niclabs/water-monitoring/2. Hito Homologación/all_ec/data/README.md

# 2020-10-22 EC data series

- `2020-10-22_real_ec.csv`: Real EC value (given by the calibration solution)
- `2020-10-22_data_ECGravity.csv`: Analog value from Gravity: Analog Electrical Conductivity Sensor (read from ADC, value in mV)
- `2020-10-22_data_TDSGravity1.csv`: Analog value from DFRobot Gravity: Analog TDS Sensor #1 (read from ADC, value in mV)
- `2020-10-22_data_TDSGravity2.csv`: Analog value from DFRobot Gravity: Analog TDS Sensor #2 (read from ADC, value in mV)
- `2020-10-22_data_multiparametro.csv`: EC value from Hach multiparameter sensor.
