niclabs/water-monitoring/2. Hito Homologación/all_ec/data3/README.md

# 2020-11-02 EC data series
`2020-11-02_tds.csv` columns:
- `N`: Row number.
- `MultiP.1`: EC value from Hach multiparameter sensor measured at the same solution as DFRobot Gravity: Analog TDS Sensor #1.
- `TDS.1`: Analog value from DFRobot Gravity: Analog TDS Sensor #1 (read from ADC, value in mV).
- `MultiP.2`: EC value from Hach multiparameter sensor measured at the same solution as DFRobot Gravity: Analog TDS Sensor #2.
- `TDS.2`: Analog value from DFRobot Gravity: Analog TDS Sensor #2 (read from ADC, value in mV).
- `T1`: Temperature (°C) value from Hach multiparameter sensor measured at the same solution as DFRobot Gravity: Analog TDS Sensor #1.
- `T2`: Temperature (°C) value from Hach multiparameter sensor measured at the same solution as DFRobot Gravity: Analog TDS Sensor #2.
- `Sol`: Calibration solution used at the data point (optional, in uS/cm)
- `Comm`: Comment
