niclabs/water-monitoring/2. Hito Homologación/all_temperature/data/README.md

# All temperature data
- `2020-10-07_all_temperature.txt`: Temperature (°C) measured with the multiparameter (reference)
- `2020-10-07_data_sensores_homologacion.csv`: Measured data (t [ms] since start, temperature by sensors, ADC read from thermistor)
