niclabs/water-monitoring/2. Hito Homologación/all_ec/data2/plot_tds_fit_ec_vs_ec.png

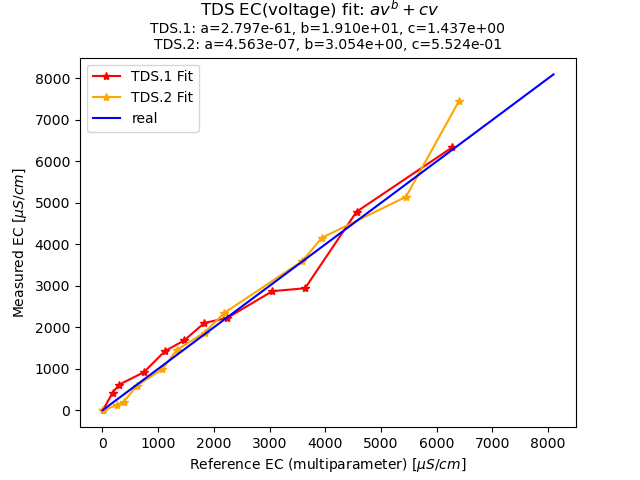
2. Hito Homologación/all_ec/data2/plot_tds_fit_ec_vs_ec.png
