niclabs/water-monitoring/2. Hito Homologación/all_ec/data/affine_plot_abserr_vs_time.png

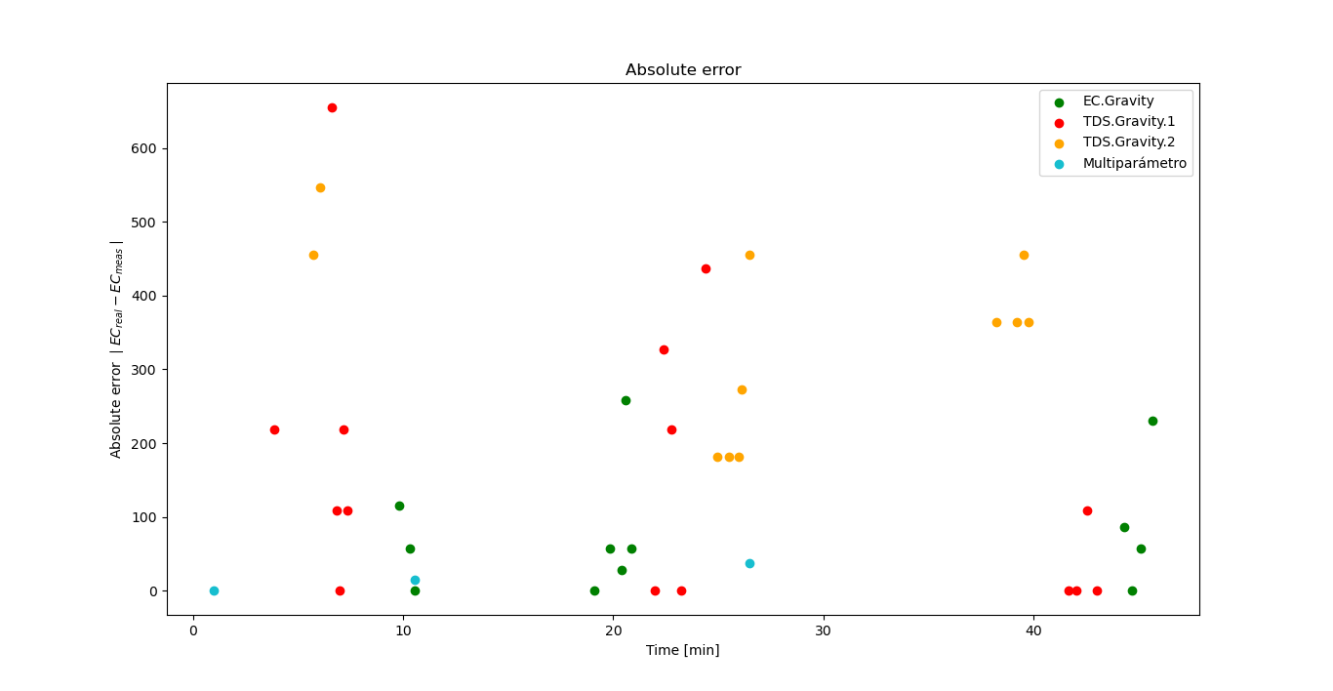
2. Hito Homologación/all_ec/data/affine_plot_abserr_vs_time.png
