niclabs/water-monitoring/2. Hito Homologación/all_ec/data/affine_plot_ec_err_comparison.png

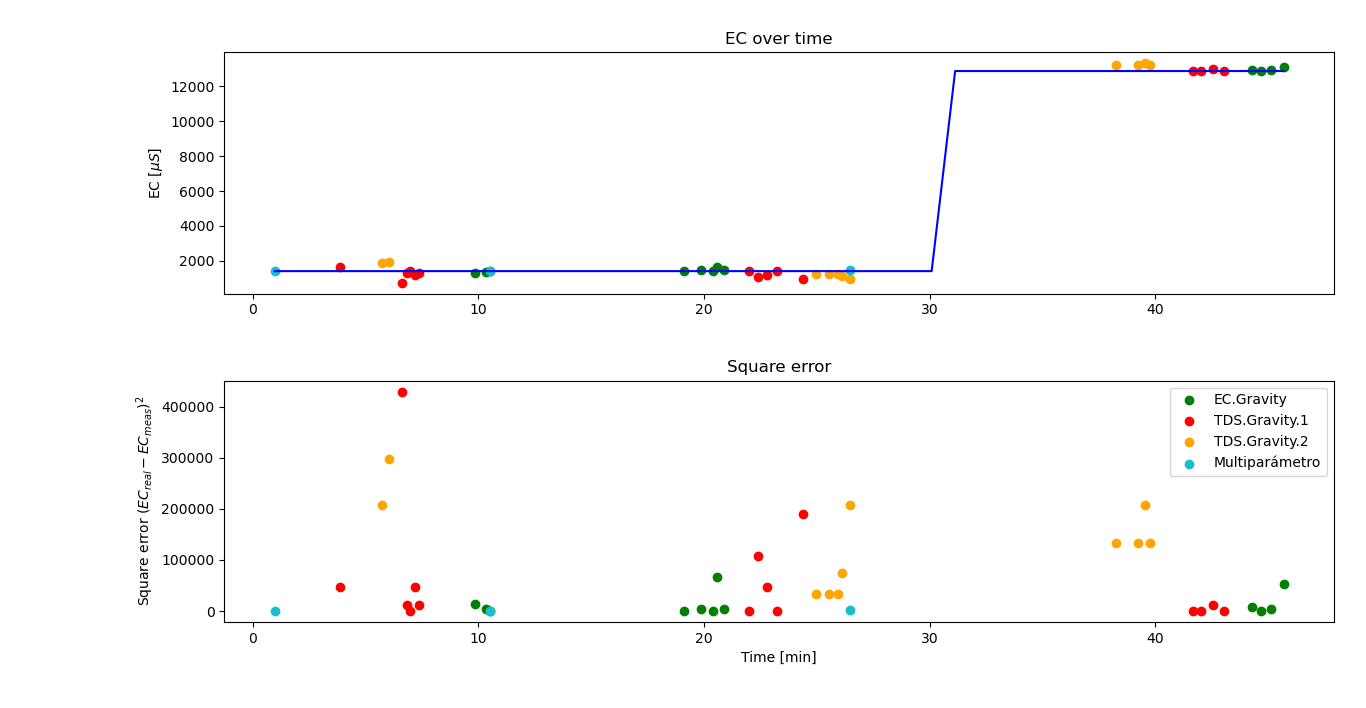
2. Hito Homologación/all_ec/data/affine_plot_ec_err_comparison.png
