niclabs/water-monitoring/2. Hito Homologación/all_ec/data/affine_plot_ec_vs_ec.png

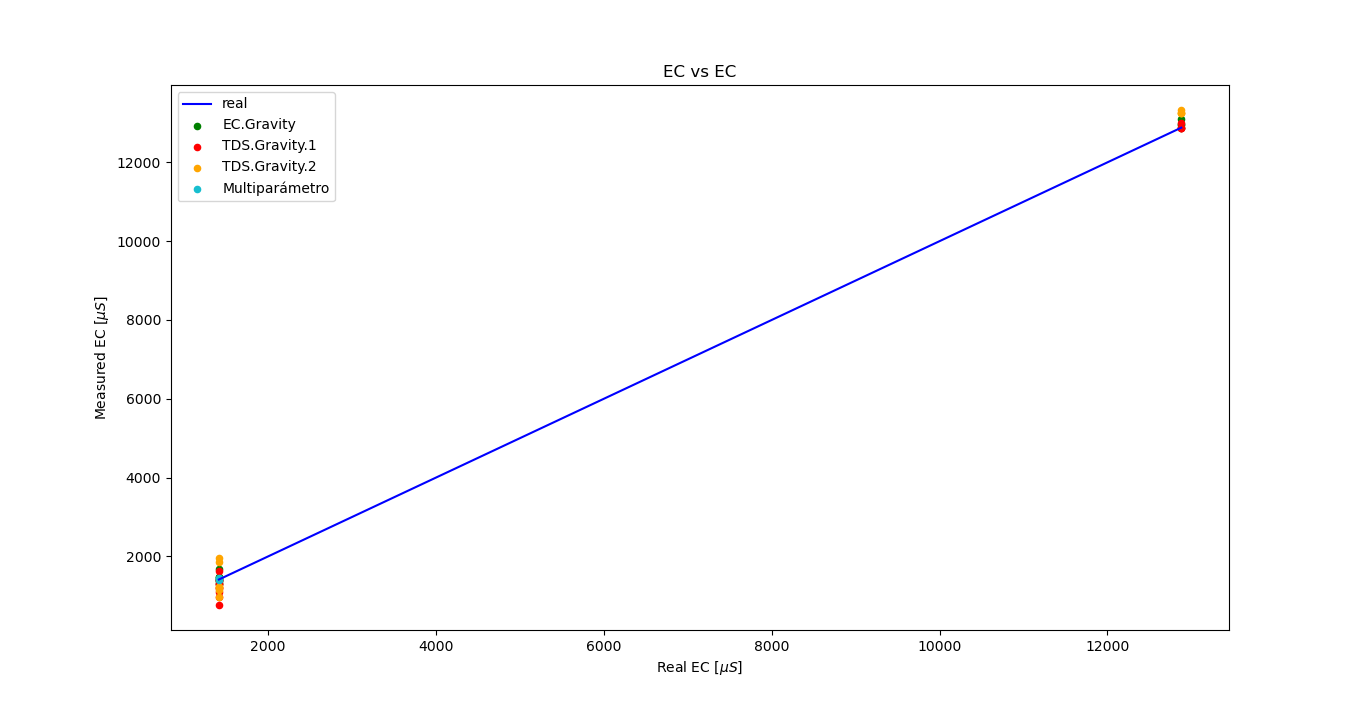
2. Hito Homologación/all_ec/data/affine_plot_ec_vs_ec.png
