niclabs/water-monitoring/2. Hito Homologación/all_ec/data/plot_ec_vs_ec_low.png

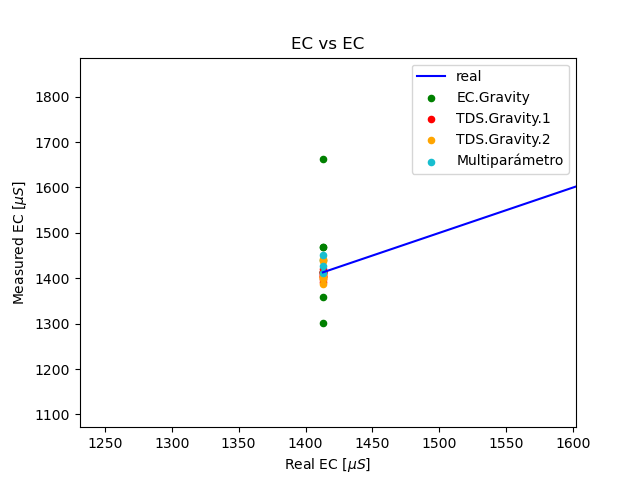
2. Hito Homologación/all_ec/data/plot_ec_vs_ec_low.png
