niclabs/water-monitoring/2. Hito Homologación/all_ec/data/plot_err_vs_time.png

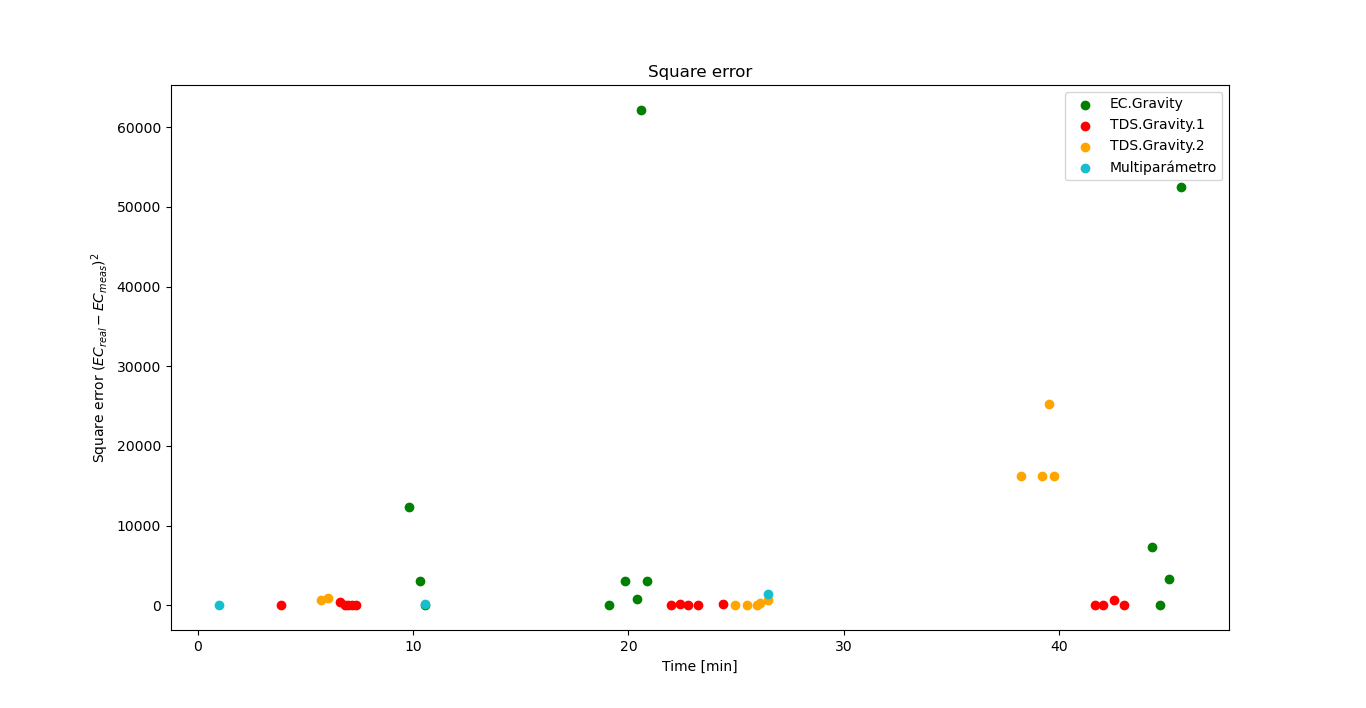
2. Hito Homologación/all_ec/data/plot_err_vs_time.png
