niclabs/water-monitoring/2. Hito Homologación/all_ph/data/plot_ph_vs_ph.png

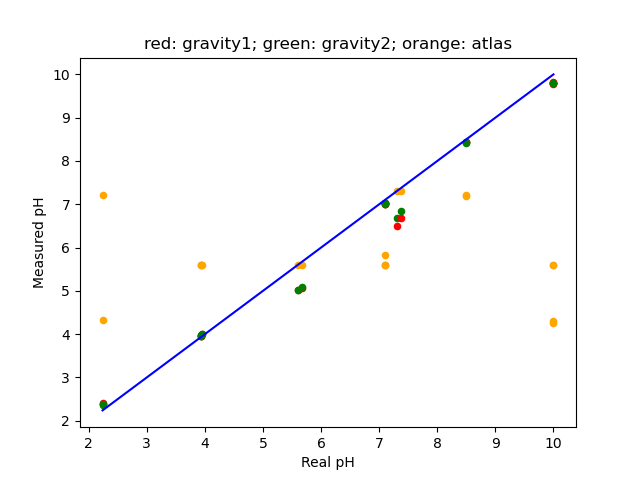
2. Hito Homologación/all_ph/data/plot_ph_vs_ph.png
