niclabs/water-monitoring/2. Hito Homologación/all_temperature/data/plot_temp_vs_temp.png

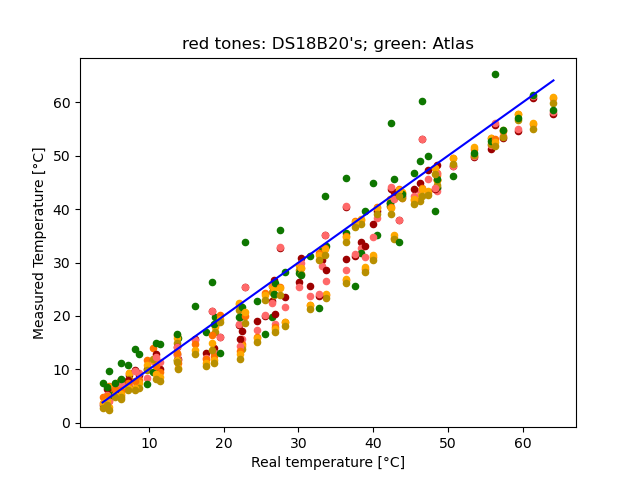
2. Hito Homologación/all_temperature/data/plot_temp_vs_temp.png
