niclabs/water-monitoring/3. Hito Energía/current_data/img/arduino_5m_5v_base.png

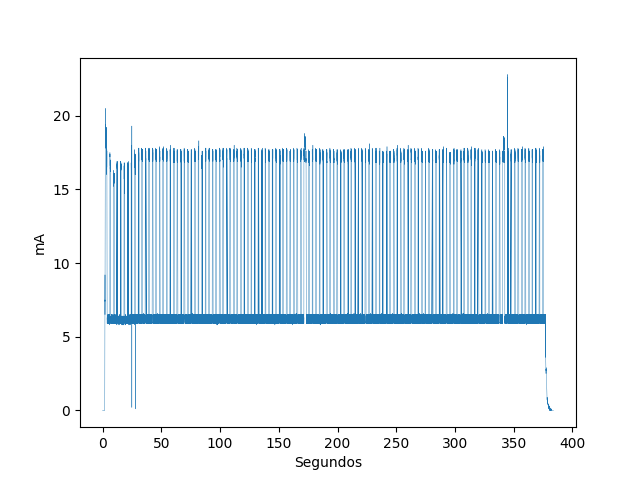
3. Hito Energía/current_data/img/arduino_5m_5v_base.png
