niclabs/water-monitoring/3. Hito Energía/current_data/img/arduino_5m_5v_rep.png

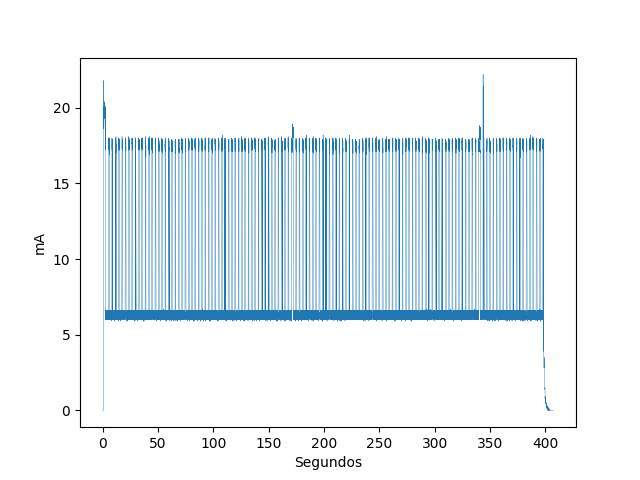
3. Hito Energía/current_data/img/arduino_5m_5v_rep.png
