niclabs/water-monitoring/3. Hito Energía/current_data/img/corriente_5m_5v_dif.png

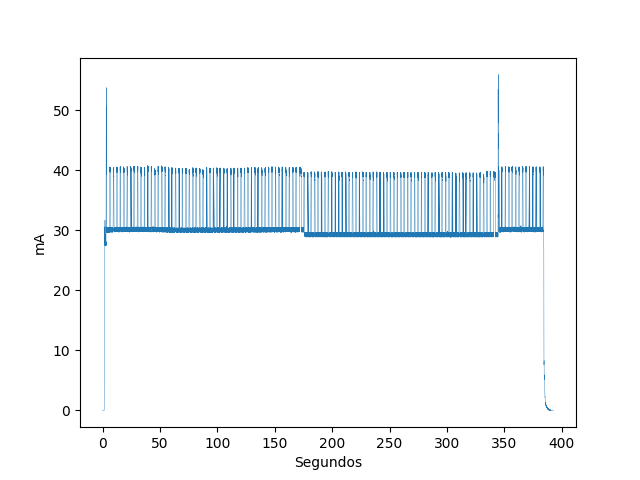
3. Hito Energía/current_data/img/corriente_5m_5v_dif.png
