niclabs/water-monitoring/3. Hito Energía/current_data/img/ds18b20_5m_5v_base.png

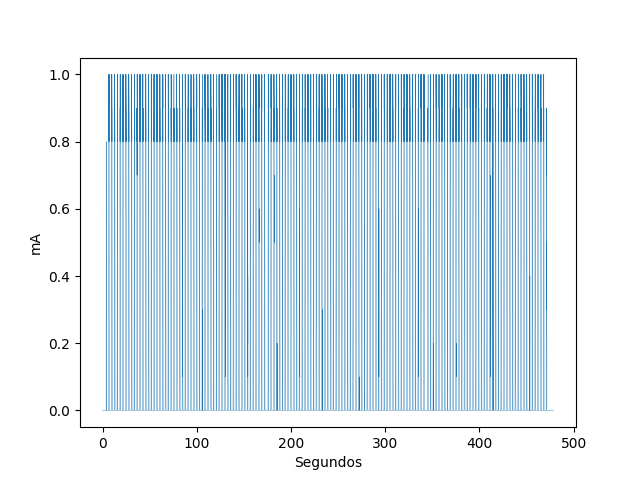
3. Hito Energía/current_data/img/ds18b20_5m_5v_base.png
