niclabs/water-monitoring/3. Hito Energía/current_data/img/fib_sleep.png

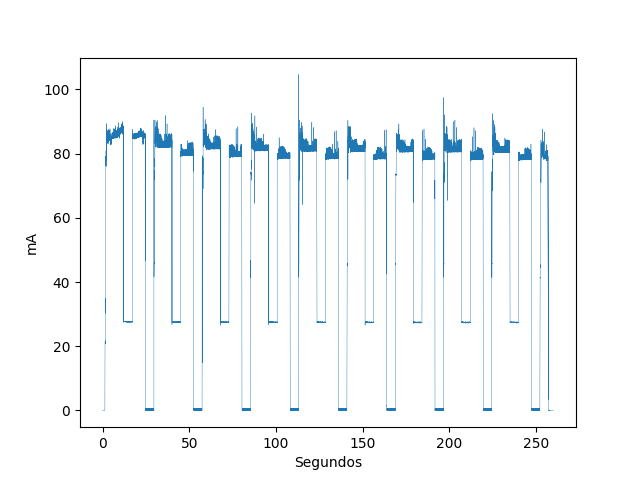
3. Hito Energía/current_data/img/fib_sleep.png
