niclabs/water-monitoring/3. Hito Energía/current_data/img/lopy_5m_5v.png

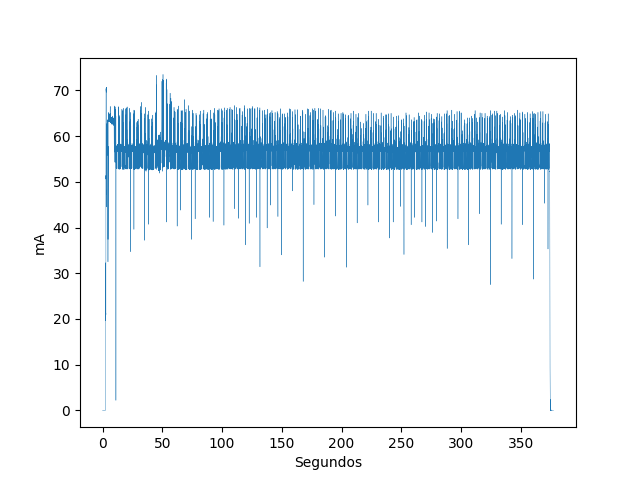
3. Hito Energía/current_data/img/lopy_5m_5v.png
