niclabs/water-monitoring/3. Hito Energía/current_data/img/lopy_5v_dif.png

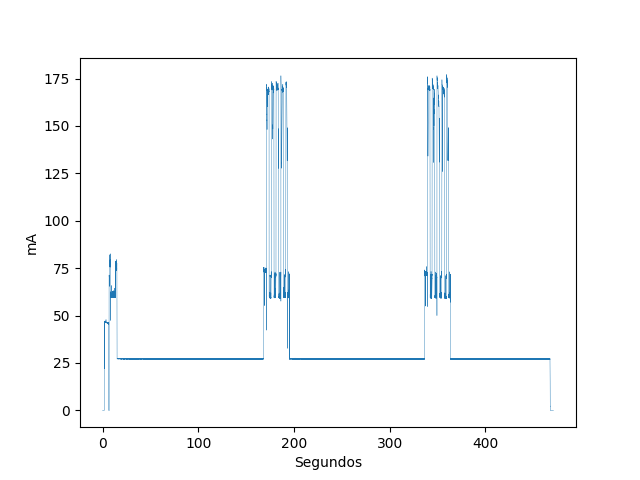
3. Hito Energía/current_data/img/lopy_5v_dif.png
