niclabs/water-monitoring/3. Hito Energía/current_data/img/lopy_envio_dif.png

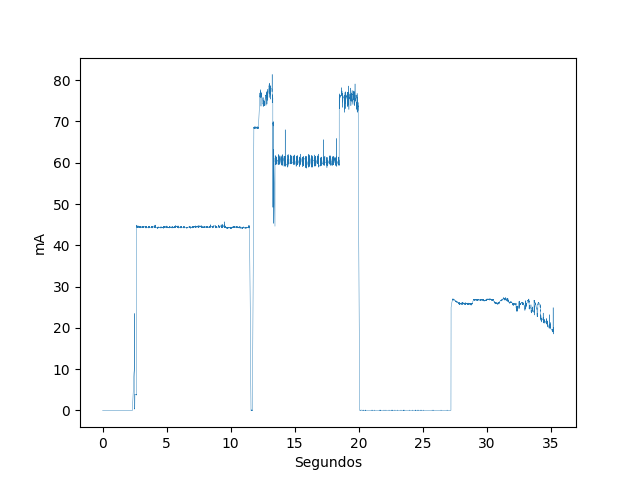
3. Hito Energía/current_data/img/lopy_envio_dif.png
