niclabs/water-monitoring/3. Hito Energía/current_data/img/rtc_5m_5v_base.png

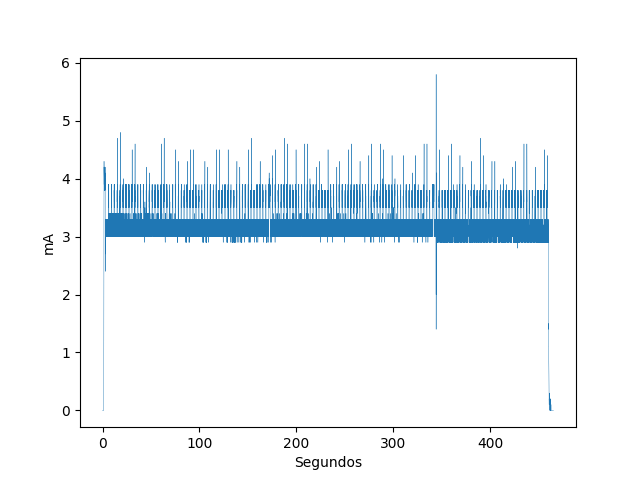
3. Hito Energía/current_data/img/rtc_5m_5v_base.png
