niclabs/water-monitoring/3. Hito Energía/current_data/img/sleep_lopy.png

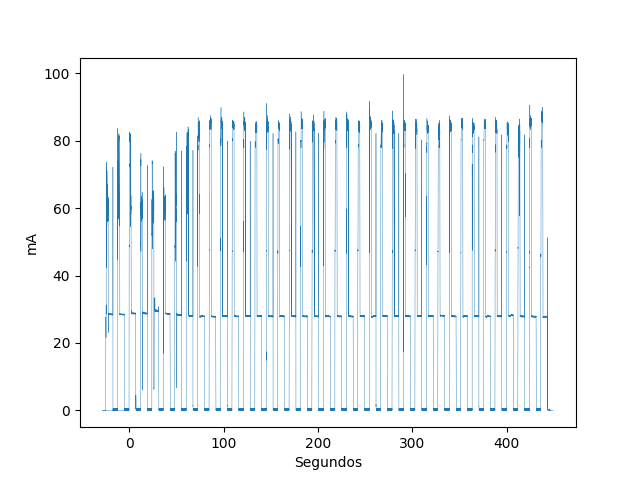
3. Hito Energía/current_data/img/sleep_lopy.png
