niclabs/water-monitoring/5. Hito Carcasa/2. Visualizaciones/Baterias.JPG

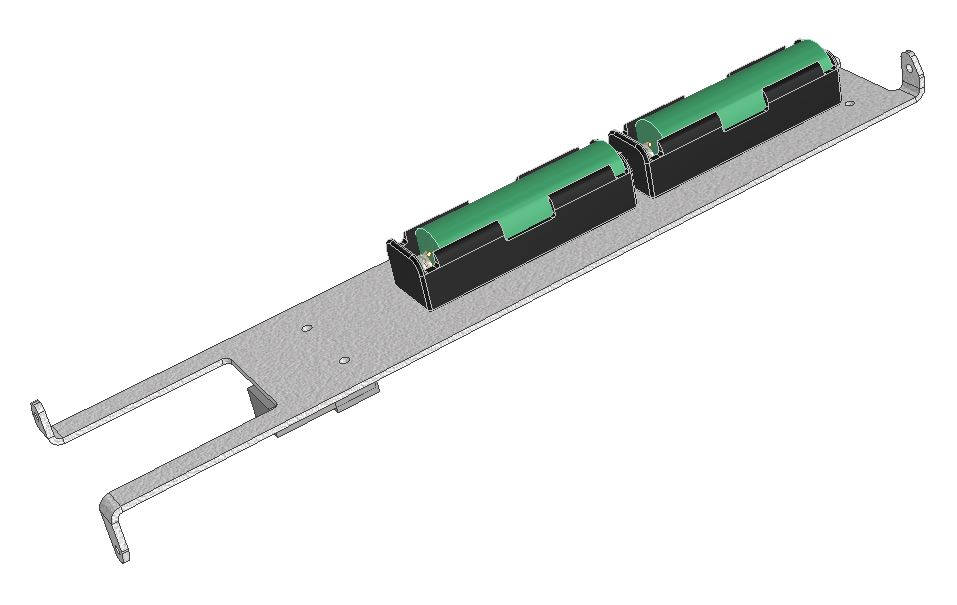
5. Hito Carcasa/2. Visualizaciones/Baterias.JPG
