niclabs/water-monitoring/5. Hito Carcasa/2. Visualizaciones/Enganche Sello.JPG

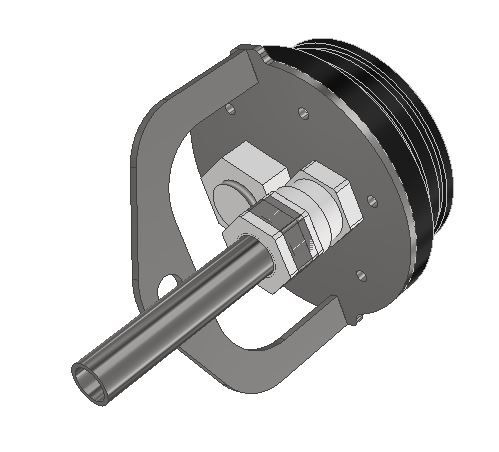
5. Hito Carcasa/2. Visualizaciones/Enganche Sello.JPG
