niclabs/water-monitoring/5. Hito Carcasa/2. Visualizaciones/Enganche.JPG

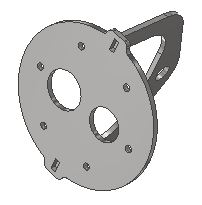
5. Hito Carcasa/2. Visualizaciones/Enganche.JPG
