niclabs/water-monitoring/5. Hito Carcasa/2. Visualizaciones/Estopa manguera.JPG

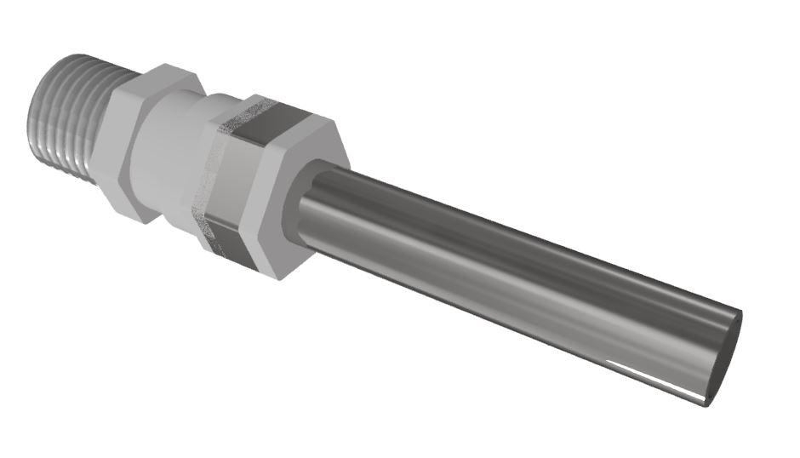
5. Hito Carcasa/2. Visualizaciones/Estopa manguera.JPG
