niclabs/water-monitoring/5. Hito Carcasa/2. Visualizaciones/Estopas enganche.JPG

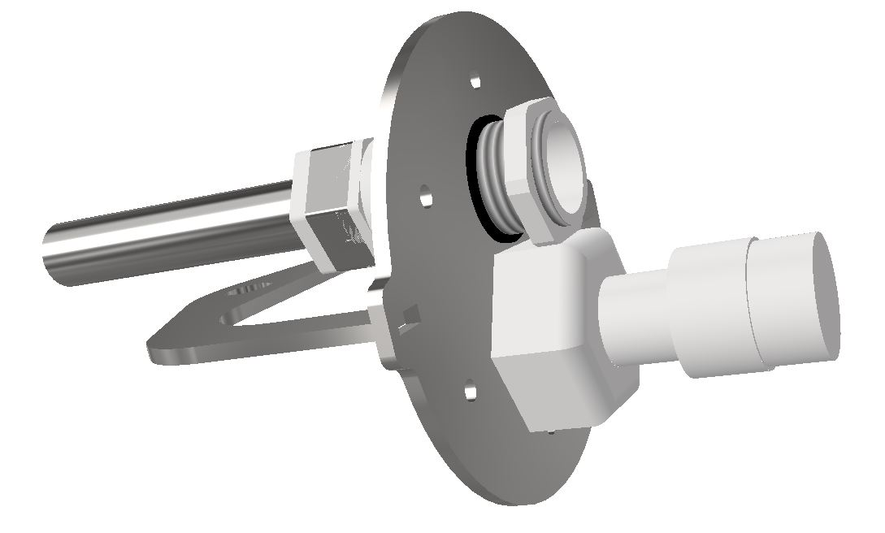
5. Hito Carcasa/2. Visualizaciones/Estopas enganche.JPG
