niclabs/water-monitoring/5. Hito Carcasa/2. Visualizaciones/Manguera Ajuste.JPG

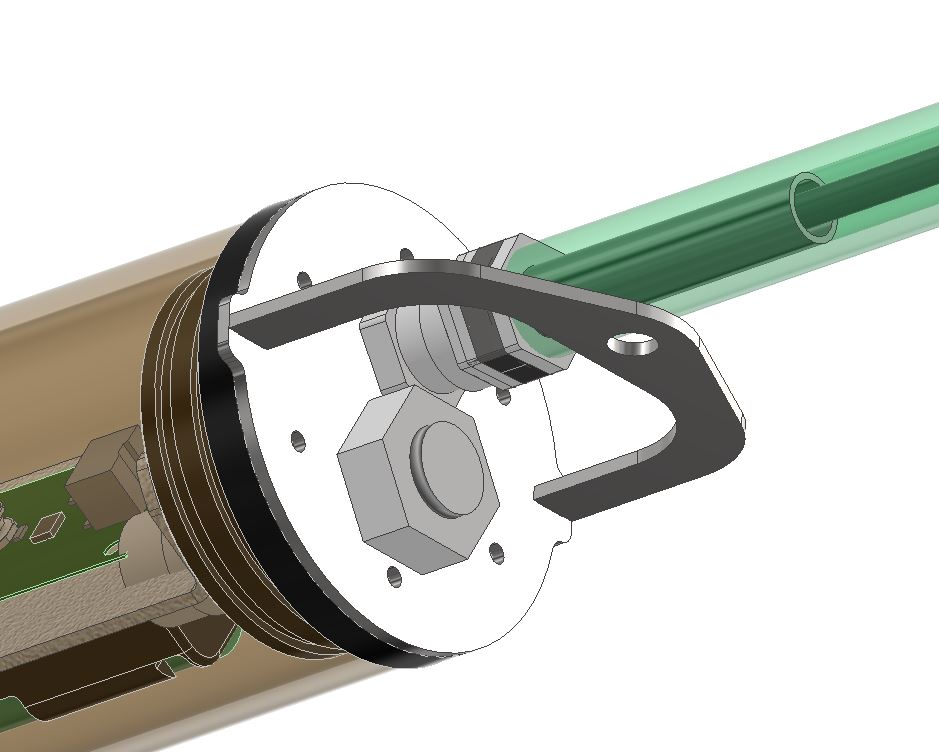
5. Hito Carcasa/2. Visualizaciones/Manguera Ajuste.JPG
