niclabs/water-monitoring/5. Hito Carcasa/2. Visualizaciones/Plataforma.JPG

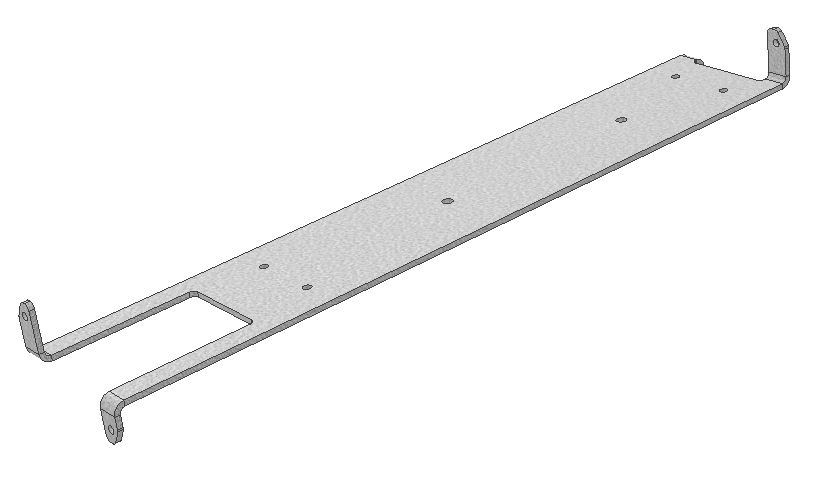
5. Hito Carcasa/2. Visualizaciones/Plataforma.JPG
