niclabs/water-monitoring/5. Hito Carcasa/2. Visualizaciones/Proteccion sello.JPG

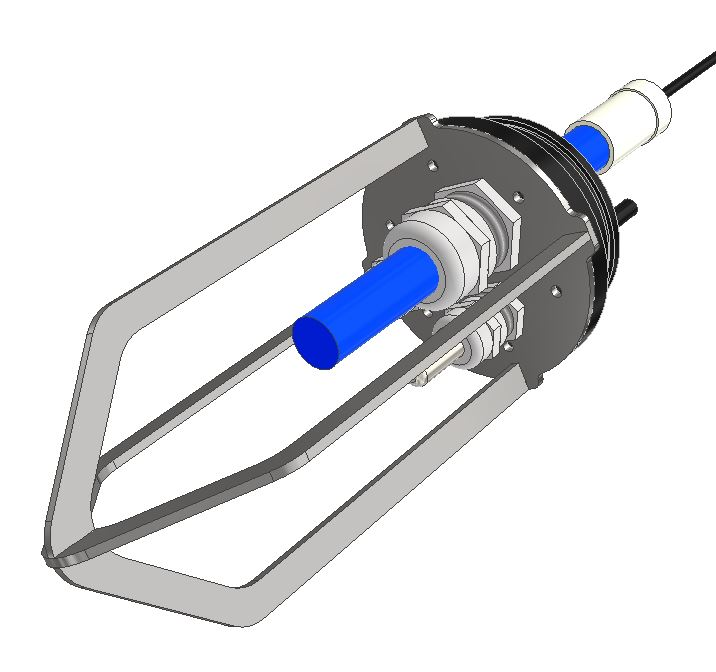
5. Hito Carcasa/2. Visualizaciones/Proteccion sello.JPG
