niclabs/water-monitoring/5. Hito Carcasa/2. Visualizaciones/Protecciขn Estopas.JPG

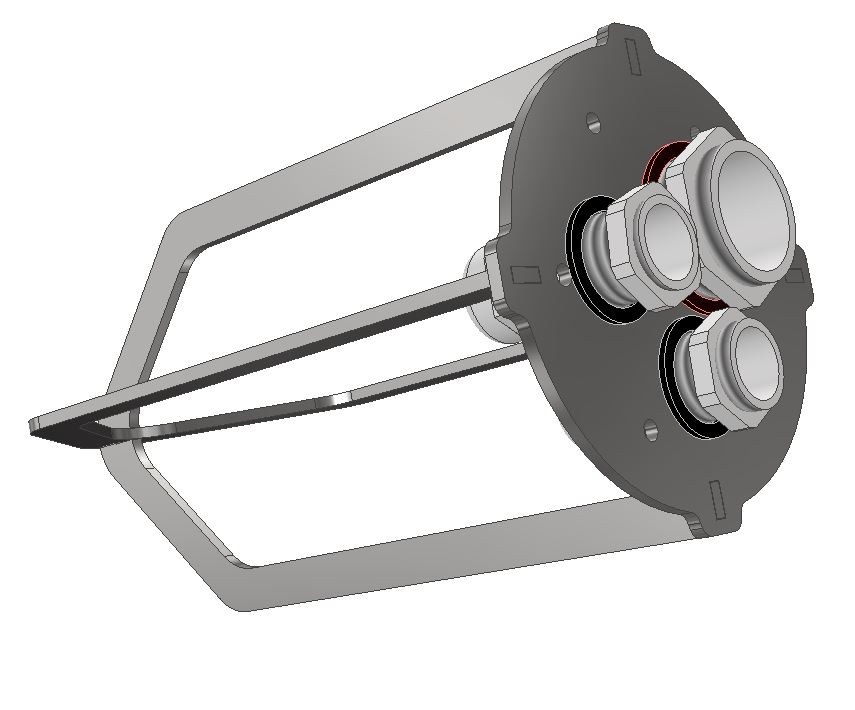
5. Hito Carcasa/2. Visualizaciones/Protecciขn Estopas.JPG
