niclabs/water-monitoring/5. Hito Carcasa/2. Visualizaciones/Protecciขn.JPG

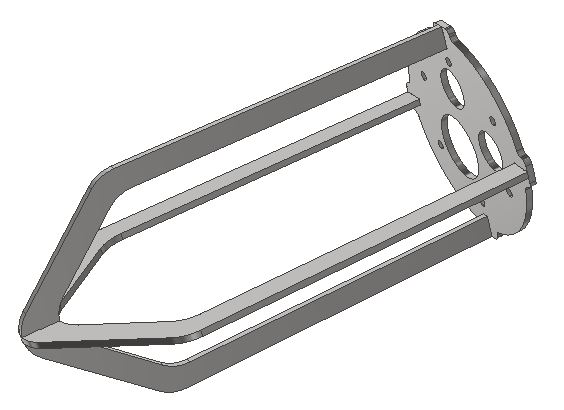
5. Hito Carcasa/2. Visualizaciones/Protecciขn.JPG
