niclabs/water-monitoring/5. Hito Carcasa/2. Visualizaciones/Sello Protrecciขn.JPG

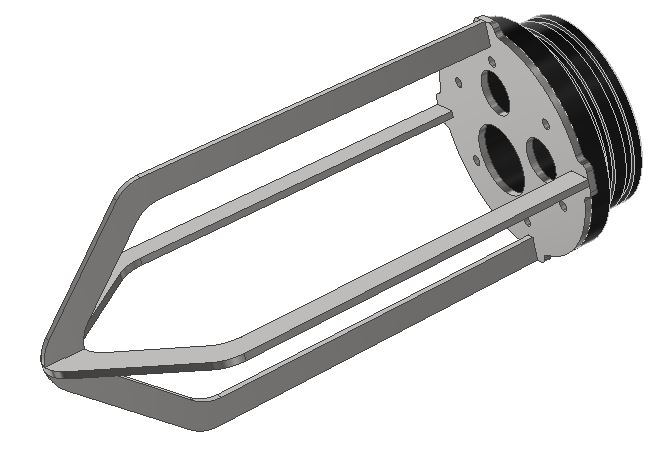
5. Hito Carcasa/2. Visualizaciones/Sello Protrecciขn.JPG
