niclabs/water-monitoring/5. Hito Carcasa/2. Visualizaciones/Sellos.JPG

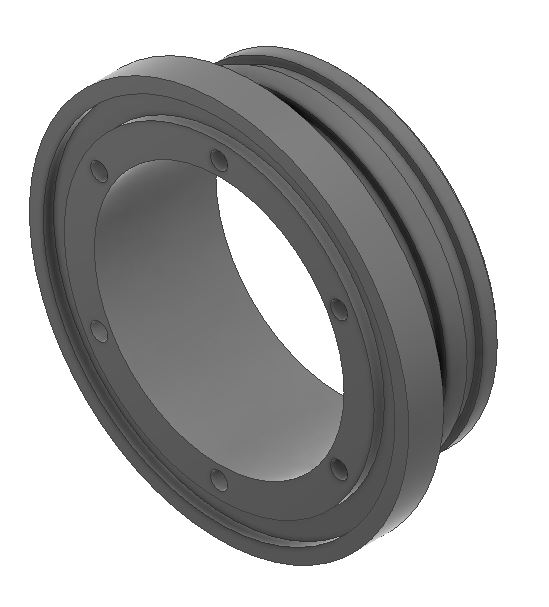
5. Hito Carcasa/2. Visualizaciones/Sellos.JPG
