niclabs/water-monitoring/5. Hito Carcasa/2. Visualizaciones/Sensores estopas.JPG

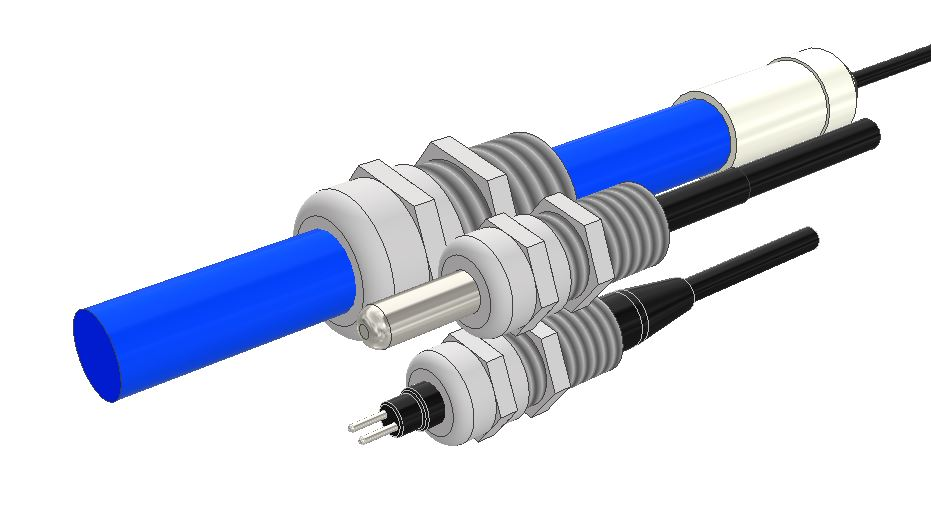
5. Hito Carcasa/2. Visualizaciones/Sensores estopas.JPG
