niclabs/water-monitoring/5. Hito Carcasa/2. Visualizaciones/Sensores Proteccion.JPG

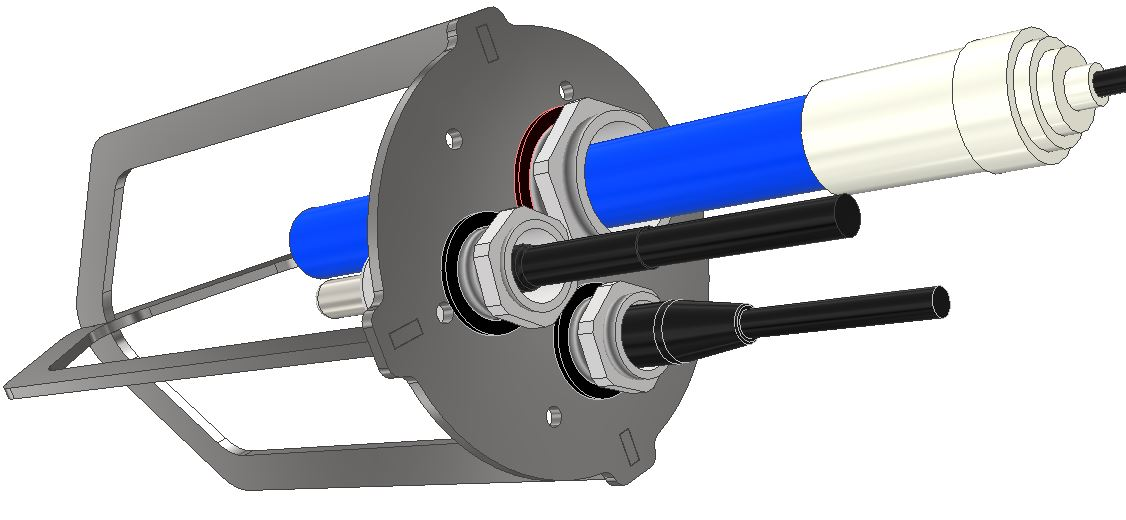
5. Hito Carcasa/2. Visualizaciones/Sensores Proteccion.JPG
