niclabs/water-monitoring/5. Hito Carcasa/2. Visualizaciones/Tubo.JPG

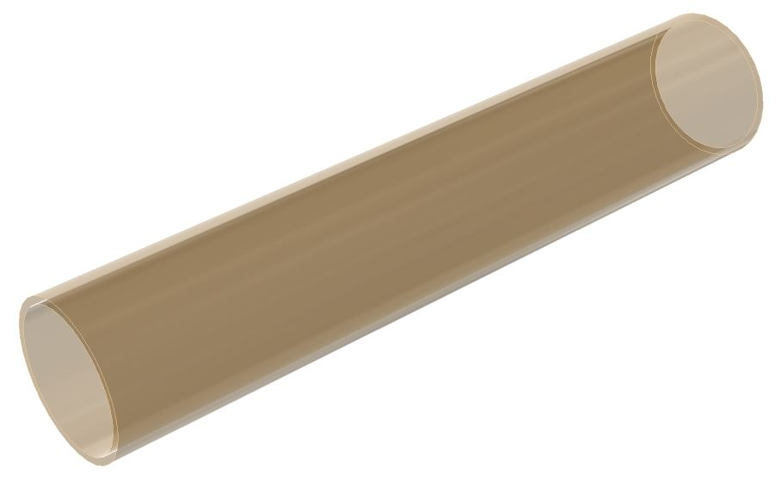
5. Hito Carcasa/2. Visualizaciones/Tubo.JPG
