niclabs/water-monitoring/docs/images/carcasa_prototipo_0.jpg

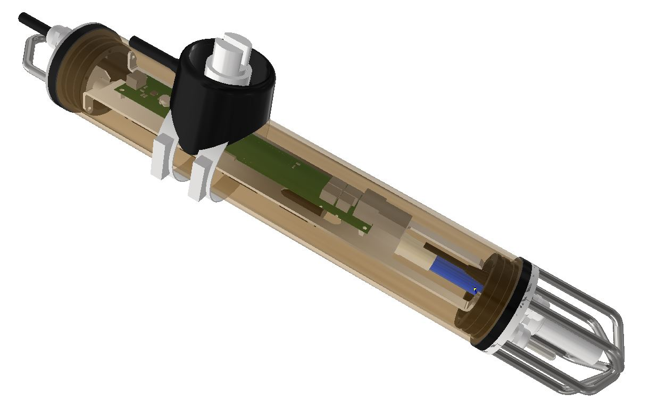
docs/images/carcasa_prototipo_0.jpg
