niclabs/water-monitoring/docs/images/carcasa_validacion_4.jpg

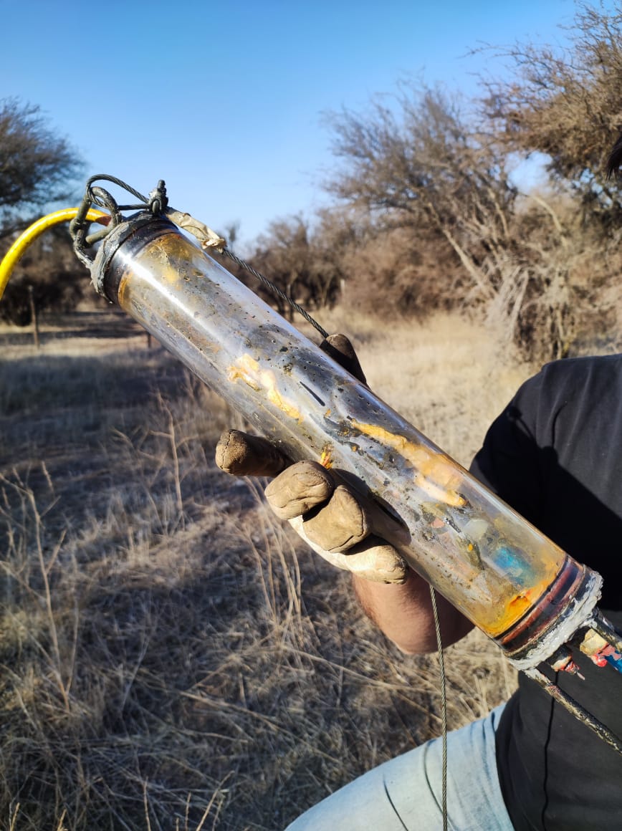
docs/images/carcasa_validacion_4.jpg
