niclabs/water-monitoring/5. Hito Carcasa/1. Planos fabricación de piezas/3. Soldaduras_Piezas acero inoxidable/Imagen referencia Enganche Flat V6.JPG

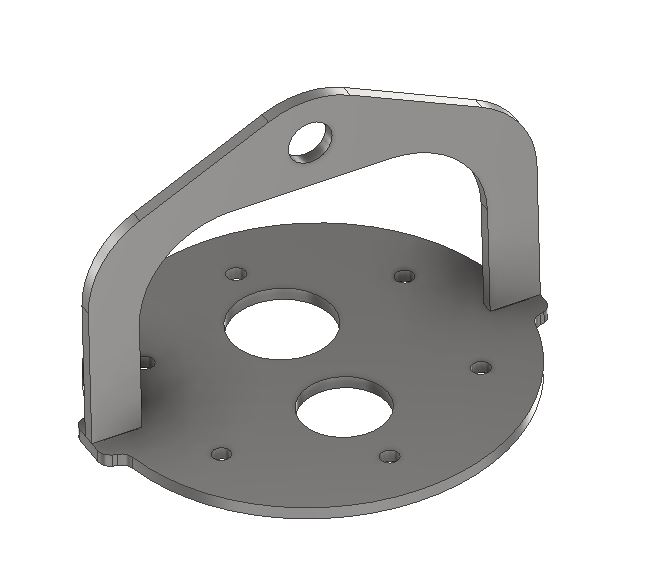
5. Hito Carcasa/1. Planos fabricación de piezas/3. Soldaduras_Piezas acero inoxidable/Imagen referencia Enganche Flat V6.JPG
