niclabs/water-monitoring/5. Hito Carcasa/1. Planos fabricación de piezas/3. Soldaduras_Piezas acero inoxidable/Union Manguera - imagen.jpeg

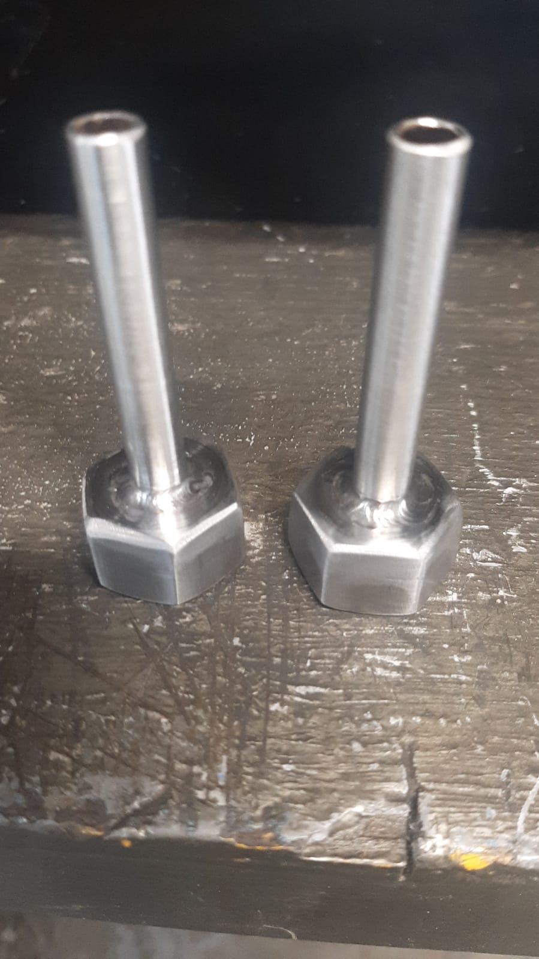
5. Hito Carcasa/1. Planos fabricación de piezas/3. Soldaduras_Piezas acero inoxidable/Union Manguera - imagen.jpeg
