niclabs/water-monitoring/5. Hito Carcasa/1. Planos fabricación de piezas/5. Caja de montaje exterior/Distribución electrónica caja.png

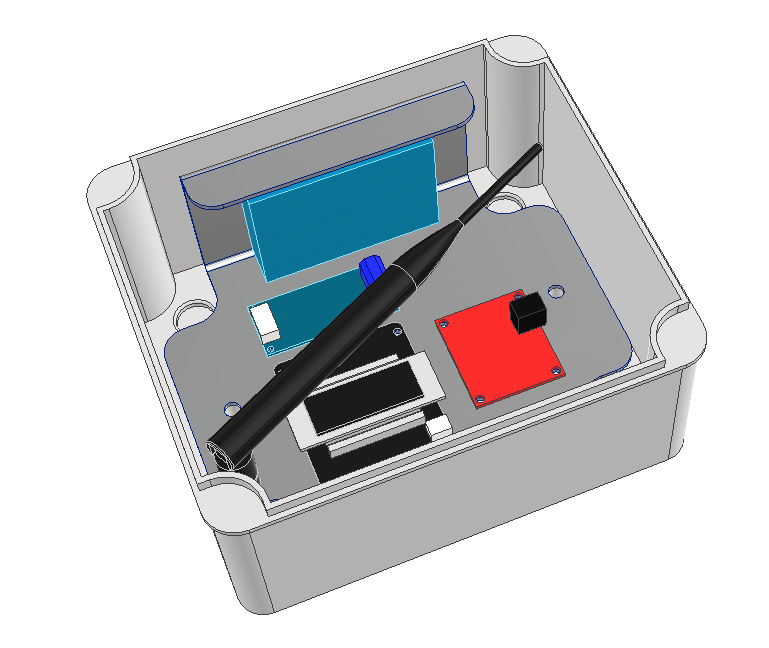
5. Hito Carcasa/1. Planos fabricación de piezas/5. Caja de montaje exterior/Distribución electrónica caja.png
