niclabs/water-monitoring/1. Hito Prototipo Datalogger/integracion/calibracion/README.md

# Calibración de los sensores.

El script de calibración permite calibrar los sensores de pH y de conductividad eléctrica (sensor de TDS), almacenando los valores de calibración en la memoria persistente del Arduino, en el cual posteriormente se puede cargar un script de sensado que utilice los valores calibrados.

## Requisitos
- Arduino Nano o compatible.
- ADC ADS1015 conectado al bus I2C del Arduino.
- Sensor [TDS Gravity](https://wiki.dfrobot.com/Gravity__Analog_TDS_Sensor___Meter_For_Arduino_SKU__SEN0244) de conductividad eléctrica conectado al canal 0 del ADC.
- Sensor [pH Gravity](https://wiki.dfrobot.com/Gravity__Analog_pH_Sensor_Meter_Kit_V2_SKU_SEN0161-V2) conectado al canal 1 del ADC.
- Sensor de temperatura DS18B20 conectado al pin digital 5 _(No olvidar la resistencia pull-up de 4.7K)_.
- Solución de referencia de pH 4.
- Solución de referencia de pH 7.
- Solución de almacenamiento de pH.
- Solución de referencia de conductividad eléctrica de 1413 uS/cm.
- Agua destilada.
- Papel absorbente (puede ser papel de cocina).
- Tres recipientes en el cual verter solución de referencia.

## Procedimiento
Una vez cargado el script de calibración, observando el monitor serial a una velocidad de 9600 se mostrará en pantalla la inicialización de cada componente conectado, y posteriormente un menú que ofrecerá opciones para calibrar el sensor de pH o el sensor de conductividad eléctrica. En la casilla de entrada, digite el número correspondiente a la opción deseada según el sensor que desee calibrar, y haga clic en __Enviar__ o __Send__. En cada opción, encontrará un submenú correspondiente a la calibración de cada sensor. Tras haber efectuado exitos

### Calibración del sensor de conductividad eléctrica (C. E.)
Al mostrarse el menú de calibración de C. E. es el momento de preparar la sonda para su calibración:
- Limpie la sonda (las puntas terminales) del sensor de C. E, y la sonda del sensor de temperatura sumergiéndolas en agua destilada.
- Seque las sondas con papel absorbente.
- En un recipiente limpio, vierta solución de referencia de 1413 uS/cm.
- Introduzca la sonda de C. E. en el recipiente, revolviendo ligeramente y procurando que las terminales queden completamente sumergidas en la solución.
- Introduzca la sonda de temperatura en el recipiente, procurando que ésta no toque las terminales de la sonda de C. E., ni queden muy juntas.
- Espere unos segundos para que el sensor de temperatura llegue al equilibrio.
- Escriba `1` en la casilla de entrada del monitor serial para entrar a la opción de `Calibrar 1413 uS/cm`, y haga clic en __Enviar__. La rutina de calibración tomará las lecturas desde los sensores.
- Si observa un mensaje con la leyenda "Fallo (¿La sonda no estaba en solucion de 1413 uS/cm?)", revise su procedimiento e inténtelo de nuevo.
- Si todo sale bien, al lado de `Calibrar 1413 uS/cm` aparecerá la etiqueta `[listo]`, en caso contrario seguirá mostrando `[NO LISTO]`.
- Escriba `9` en la casilla de entrada y haga clic en __Enviar__ para volver al menú principal.

### Calibración del sensor de pH
Al mostrarse el menú de calibración de pH es el momento de preparar la sonda para su calibración:
- Remueva el vaso protector de la sonda de pH.
- Limpie la punta del sensor de pH sumergiéndola en agua destilada.
- Seque suavelmente el exceso de agua en la punta del sensor con papel absorbente.
- En un recipiente limpio, vierta solución de referencia de pH 4, y en otro recipiente vierta solución de pH 7.
- Introduzca la sonda de pH en el recipiente con solución de pH 4, revolviendo ligeramente y procurando que las terminales queden completamente sumergidas en la solución.
- Escriba `1` en la casilla de entrada del monitor serial para entrar a la opción de `Calibrar Acido (pH 4)`, y haga clic en __Enviar__. La rutina de calibración tomará las lecturas desde el sensor. Al finalizar exitosamente esta rutina, el menú de calibración de pH mostrará la etiqueta `[listo]` al lado de `Calibrar Acido (pH 4)`. 
- Limpie nuevamente la punta del sensor de pH con agua desilada, y séquela.
- Introduzca la sonda de pH en el recipiente con solución de pH 7, revolviendo ligeramente y procurando que las terminales queden completamente sumergidas en la solución.
- Escriba `2` en la casilla de entrada del monitor serial para entrar a la opción de `Calibrar Neutro (pH 7)`, y haga clic en __Enviar__. La rutina de calibración tomará las lecturas desde el sensor. Al finalizar exitosamente esta rutina, el menú de calibración de pH mostrará la etiqueta `[listo]` al lado de `Calibrar Neutro (pH 7)`.
- Una vez finalizado el procedimiento, descarte el contenido del vaso protector de la sonda de pH, y llene el vaso protector con solución de almacenamiento.
- Introduzca la sonda de pH en el vaso protector, cuidando que ésta se mantenga húmeda.

## Consideraciones técnicas
El script que utilice posteriormente las calibraciones almacenadas por este procedimiento debe buscar los valores en la misma dirección de memoria en que fueron almacenados en la EEPROM. Si las calibraciones parecen perderse, revise el valor de la macro `ADDR_OFFSET` y los índices con los que se instancian las librerías de los sensores. Por ejemplo, si en el script de calibración la librería de pH se instancia
```c++
#define ADDR_OFFSET 50
...
DFRobot_PH phGravity(ADDR_OFFSET+2);
```
entonces en el script que utilice esta calibración del sensor de pH también debe instanciar la librería de pH con el índice 52.
