niclabs/water-monitoring/2. Hito Homologación/all_ec/data2/plot_tds_characteristic.png

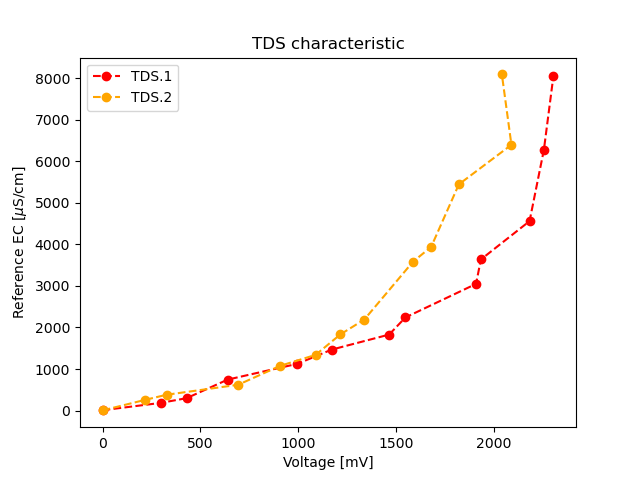
2. Hito Homologación/all_ec/data2/plot_tds_characteristic.png
