niclabs/water-monitoring/3. Hito Energía/lopy_serial_sd_and_bmp280/LoPy4_sd/boot.py

import os
import machine
import pycom
import socket
import ubinascii
import struct
import uctypes
from network import LoRa
from network import Sigfox
from machine import UART
import time
import math
from machine import Pin
from lib.error_check import check_fletcher16
from payload_decoder import decode_payload
from bmp280 import *

# UNCOMMENT FOR REAL LORA
"""
print('========== Starting LoRaWAN configuration ==========')
lora = LoRa(mode=LoRa.LORAWAN, region=LoRa.AU915, adr=False)
print(ubinascii.hexlify(lora.mac()).upper())
# create an ABP authentication params
dev_addr = struct.unpack(">l", ubinascii.unhexlify('2603106C'))[0]
nwk_swkey = ubinascii.unhexlify('76DB5271CDE78981299F45763A8D92DF')
app_swkey = ubinascii.unhexlify('CA973AAF7951401122434BD66A6E8B6A')
# create an OTAA authentication params
# app_eui = ubinascii.unhexlify('0000000000000000')
# app_key = ubinascii.unhexlify('7557FCC7BB76CAC19E35D858FD1E60E0')

# Remove unused channels
for i in range(0,8):
    lora.remove_channel(i)
for i in range(16,65):
    lora.remove_channel(i)
for i in range(66,72):
    lora.remove_channel(i)

# join a network using ABP (Activation By Personalization)
lora.join(activation=LoRa.ABP, auth=(dev_addr, nwk_swkey, app_swkey))
#lora.join(activation=LoRa.OTAA, auth=(app_eui, app_key), timeout=0)

# wait until the module has joined the network
while not lora.has_joined():
    time.sleep(2.5)
    print('Not yet joined...')
print("LoPy4 - Has joined!!!!!")

# create a LoRa socket
s = socket.socket(socket.AF_LORA, socket.SOCK_RAW)

# set the LoRaWAN socket options
DATA_RATE = 0
s.setsockopt(socket.SOL_LORA, socket.SO_DR, DATA_RATE)
s.setsockopt(socket.SOL_LORA, socket.SO_CONFIRMED, True)
"""

# <COMMENT THIS FOR REAL LORA>
DATA_RATE = 0

print('########## CREATING FAKE LORA SOCKET (for SD testing) ###########')
class NullSocket:
    def setblocking(self, *args):
        pass
    def send(self, *args):
        pass
s = NullSocket()
# </COMMENT THIS FOR REAL LORA>

print('========== Opening BMP280 Pressure sensor ===========')
i2c = machine.I2C()
bmp = BMP280(i2c)
# https://github.com/dafvid/micropython-bmp280
bmp.use_case(BMP280_CASE_HANDHELD_LOW)

print('========== Opening Expansion board SD Reader ===========')
SD_MOUNT_POINT = '/sd_mnt'
MAX_FILE_SIZE = 1024*1024 # Files no much more than 1MB
# https://docs.pycom.io/firmwareapi/pycom/machine/sd/
sd = machine.SD()
os.mount(sd, SD_MOUNT_POINT)
file_index = len(os.listdir(SD_MOUNT_POINT)) # Always a fresh index

#SD_BLOCK_SIZE = 512
#sd_buffer = bytearray(SD_BLOCK_SIZE)

print('========== Starting Serial UART configuration ===========')
# Configure second UART bus on pins P3(TX1) and P4(RX1)
print('[boot.py before uart] SD dir contents at', SD_MOUNT_POINT, ':', os.listdir(SD_MOUNT_POINT))
uart = machine.UART(1, baudrate=19200, bits=8, parity=None, stop=1, pins=('P3', 'P6'))
print('[boot.py after uart] SD dir contents at', SD_MOUNT_POINT, ':', os.listdir(SD_MOUNT_POINT))
# Si el contenido de la carpeta no es el mismo, probablemente UART está pisando
# alguno de los pines que necesita la LoPy para hablar con la SD:
# https://docs.pycom.io/firmwareapi/pycom/machine/sd/ 

print('========== Starting PIN wakeup configuration ============')
#p_in = Pin('P10', mode=Pin.OUT, pull=None, alt=-1)
# P4 lo usa la tarjeta de expansión para SD
# https://docs.pycom.io/firmwareapi/pycom/machine/#
#machine.pin_sleep_wakeup(['P4'], machine.WAKEUP_ALL_LOW, False) 
machine.pin_sleep_wakeup(['P6'], machine.WAKEUP_ALL_LOW, False)
#machine.enable_irq()

pycom.heartbeat(False)

time.sleep(5)

machine.main('main.py')
print('========== Starting main.py ==========')
